dougli1sqrd/astro-medallion/local/Aquarius_symbol_(fixed_width).svg.png

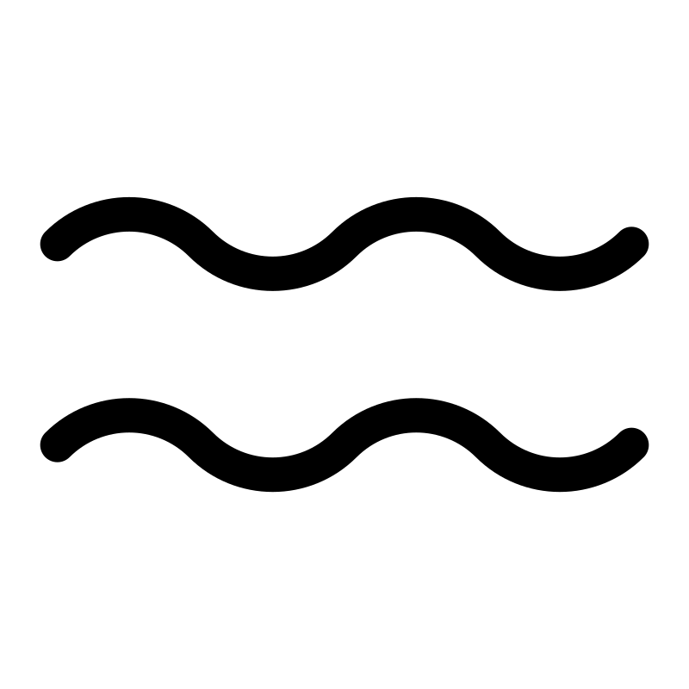
local/Aquarius_symbol_(fixed_width).svg.png
