dougli1sqrd/astro-medallion/local/Gemini_symbol_(fixed_width).svg.png

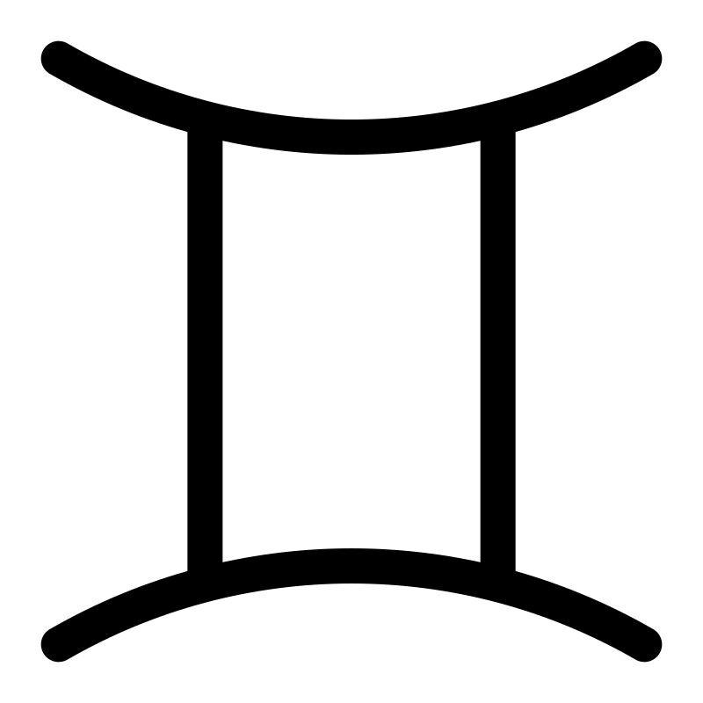
local/Gemini_symbol_(fixed_width).svg.png
