dougli1sqrd/astro-medallion/local/Leo_symbol_(fixed_width).svg.png

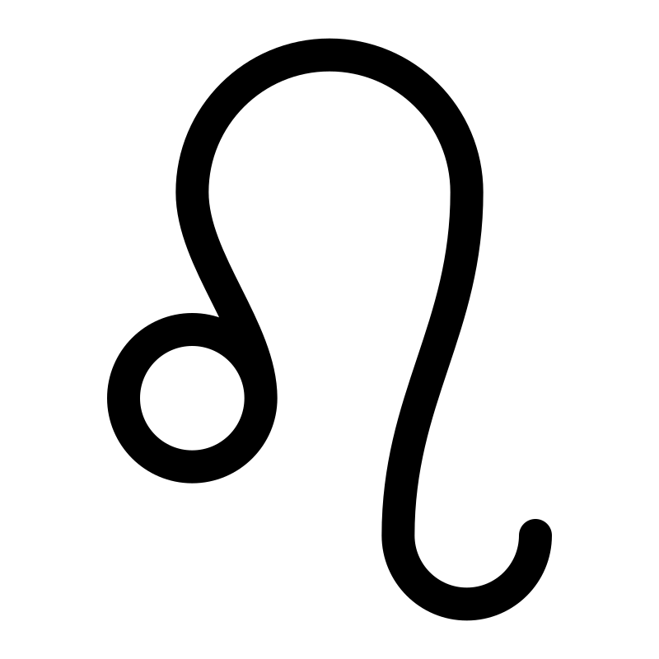
local/Leo_symbol_(fixed_width).svg.png
