dougli1sqrd/astro-medallion/local/Sagittarius_symbol_(fixed_width).svg.png

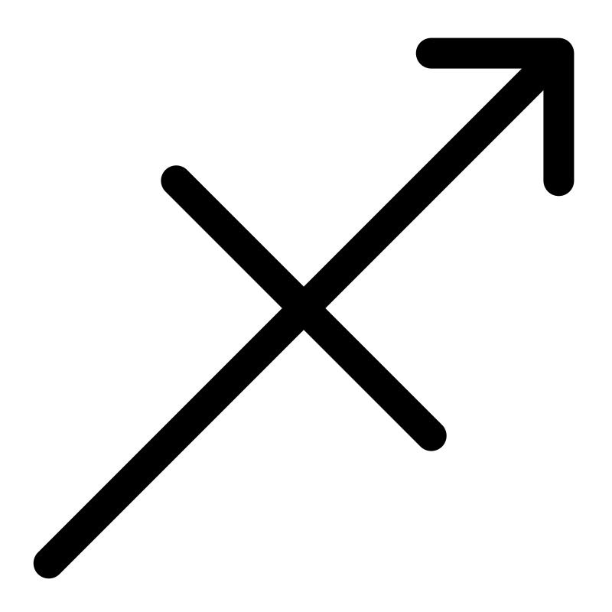
local/Sagittarius_symbol_(fixed_width).svg.png
