dougli1sqrd/astro-medallion/local/Taurus_symbol_(fixed_width).svg.png

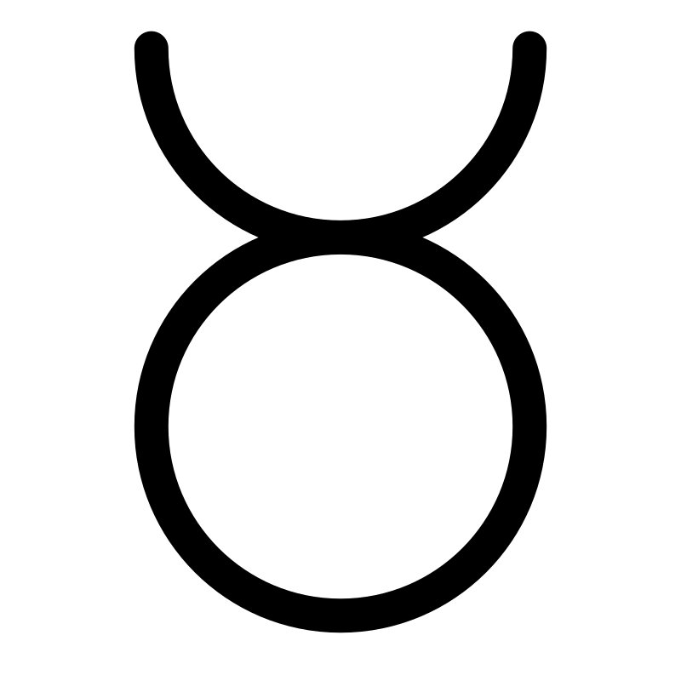
local/Taurus_symbol_(fixed_width).svg.png
